FloppyO1/Floppy_soldering_station/CASE/components/power supply/under.jpg

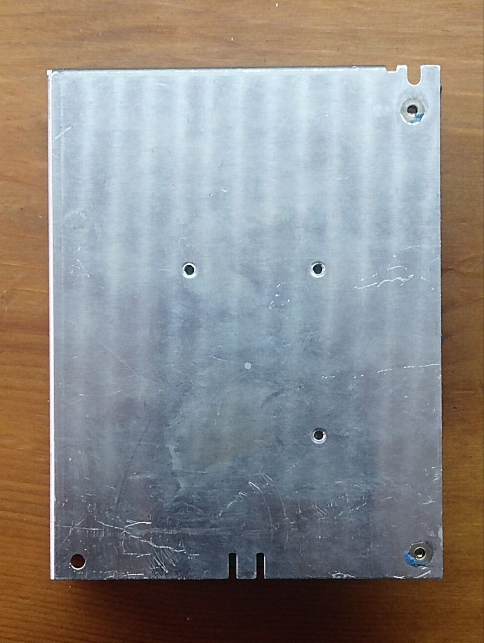
CASE/components/power supply/under.jpg
