FloppyO1/Floppy_soldering_station/CASE/components/GX16-4P.SLDPRT

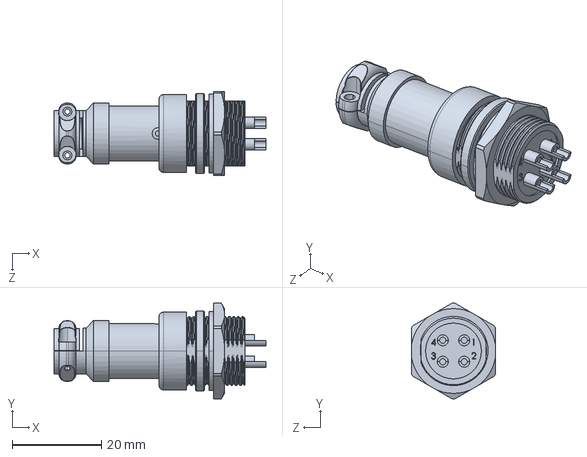
[picture p21: CAD file, 2024-06-17]
CASE/components/GX16-4P.SLDPRT
47.5 x 21.5 x 18.9 mm
