FloppyO1/Floppy_soldering_station/CASE/soldering iron holder.SLDPRT

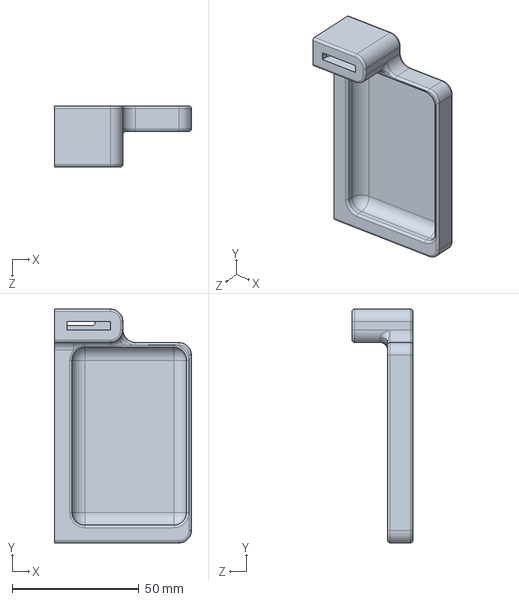
[picture p22: CAD file, 2024-06-17]
CASE/soldering iron holder.SLDPRT
54.0 x 92.2 x 24.0 mm
