FloppyO1/Floppy_soldering_station/CASE/components/C14 power plug.SLDPRT

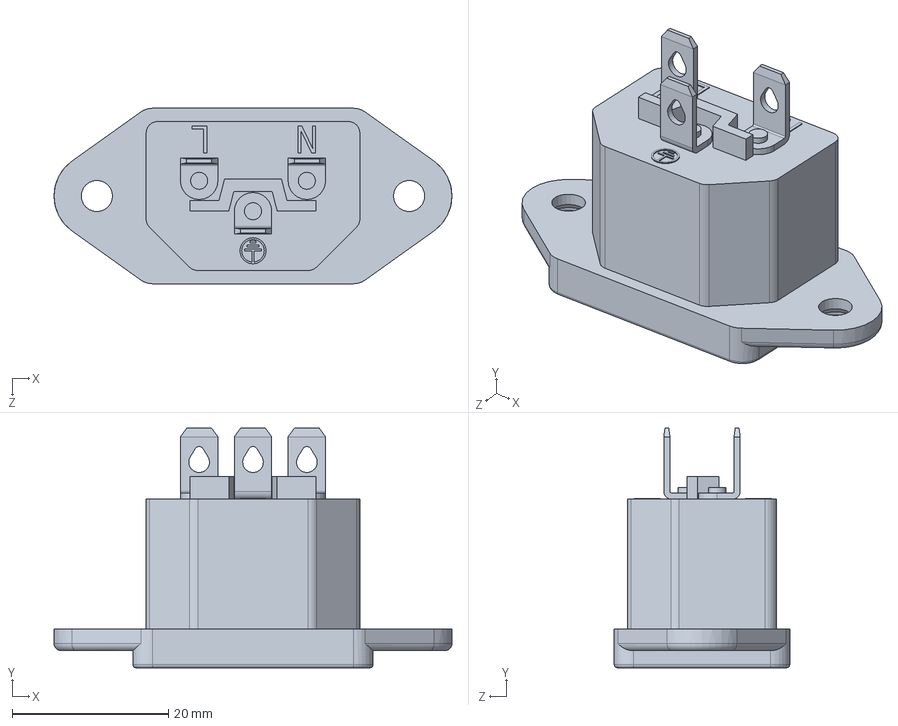
[picture p23: CAD file, 2024-06-17]
CASE/components/C14 power plug.SLDPRT
51.0 x 30.7 x 22.5 mm
