FloppyO1/Floppy_soldering_station/CASE/case 3.SLDPRT

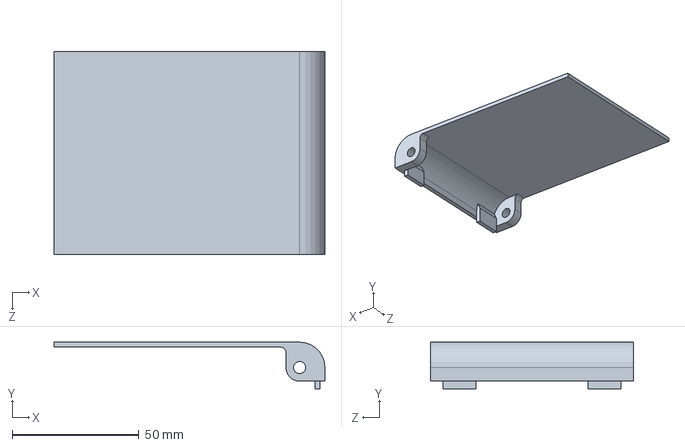
[picture p24: CAD file, 2024-06-17]
CASE/case 3.SLDPRT
106.7 x 18.4 x 80.0 mm
