FloppyO1/Floppy_soldering_station/CASE/components/rotary+encoder_17mm_hole_spc.SLDPRT

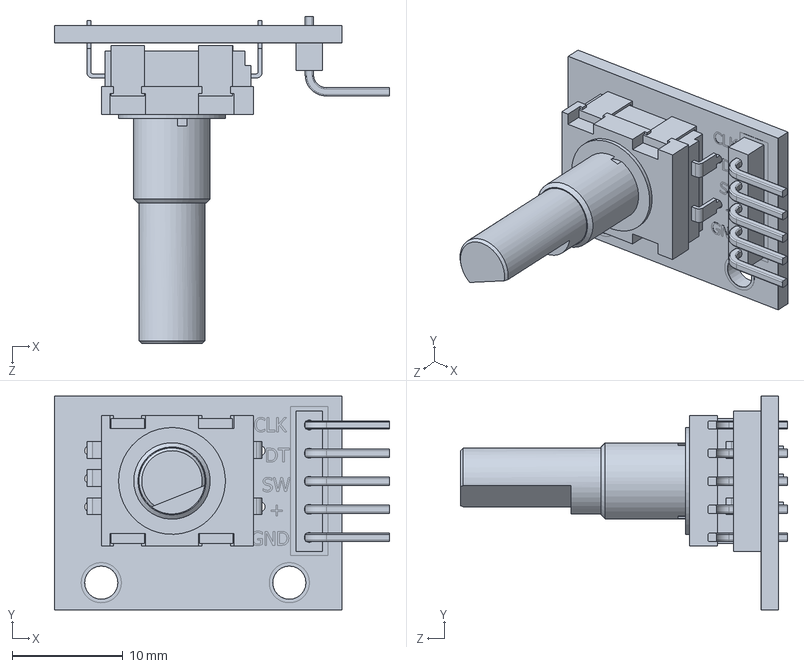
[picture p25: CAD file, 2024-06-17]
CASE/components/rotary+encoder_17mm_hole_spc.SLDPRT
30.3 x 19.3 x 29.6 mm
