FloppyO1/Floppy_soldering_station/CASE/case 1.SLDPRT

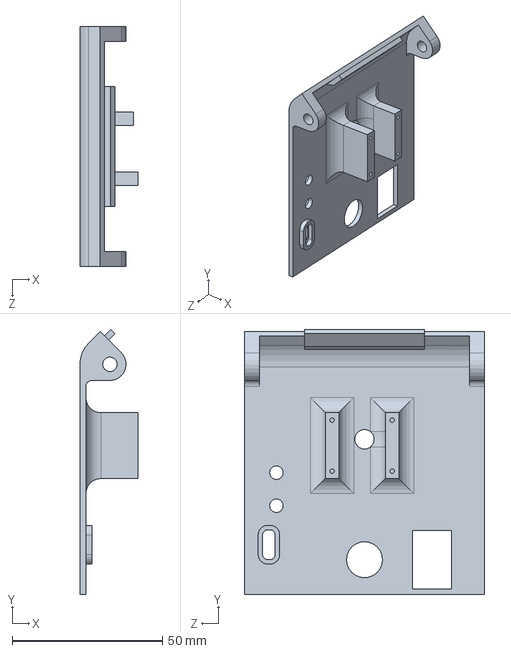
[picture p26: CAD file, 2024-06-17]
CASE/case 1.SLDPRT
19.4 x 88.3 x 80.0 mm
