FloppyO1/Floppy_soldering_station/CASE/case 2.SLDPRT

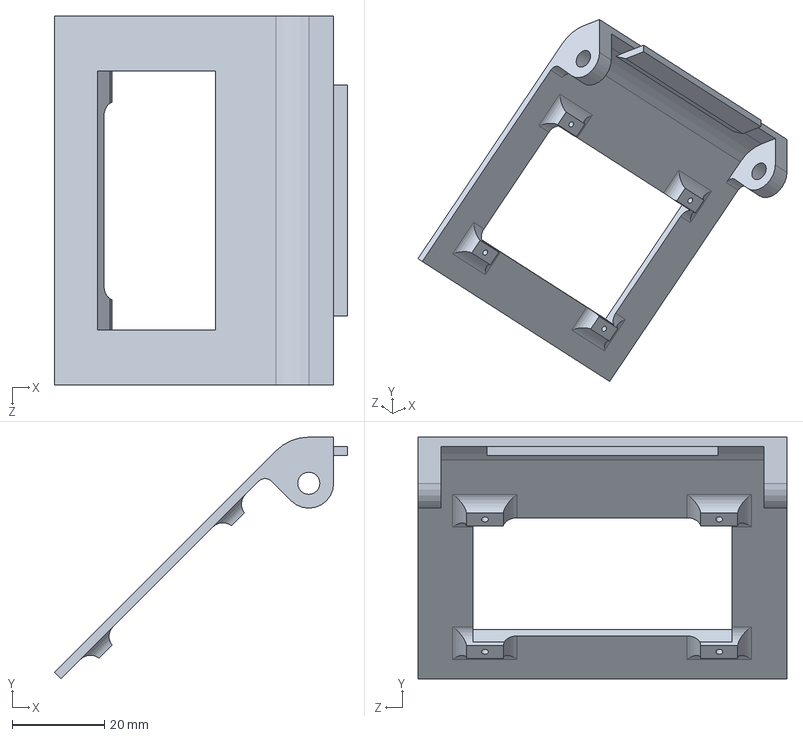
[picture p27: CAD file, 2024-06-17]
CASE/case 2.SLDPRT
63.5 x 52.4 x 80.0 mm
