FloppyO1/Floppy_soldering_station/CASE/case base.SLDPRT

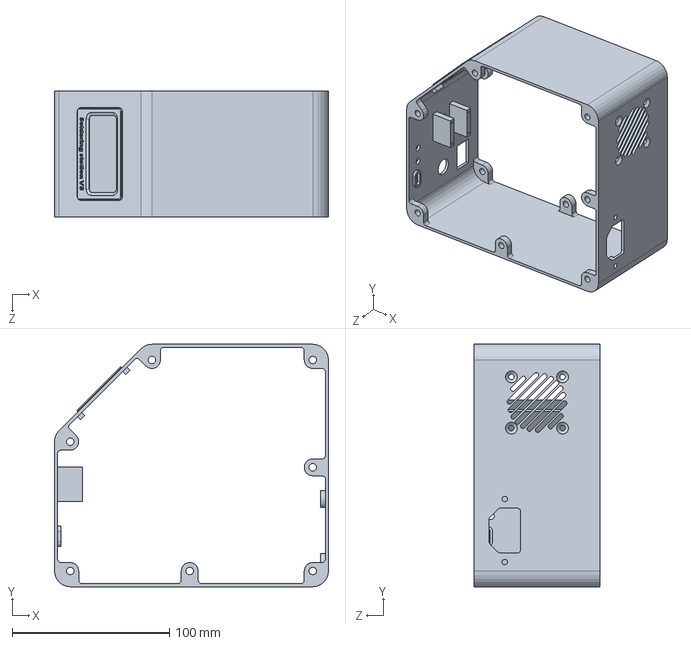
[picture p28: CAD file, 2024-06-17]
CASE/case base.SLDPRT
174.0 x 154.0 x 80.0 mm
