FloppyO1/Floppy_soldering_station/CASE/brass scourer holder.SLDPRT

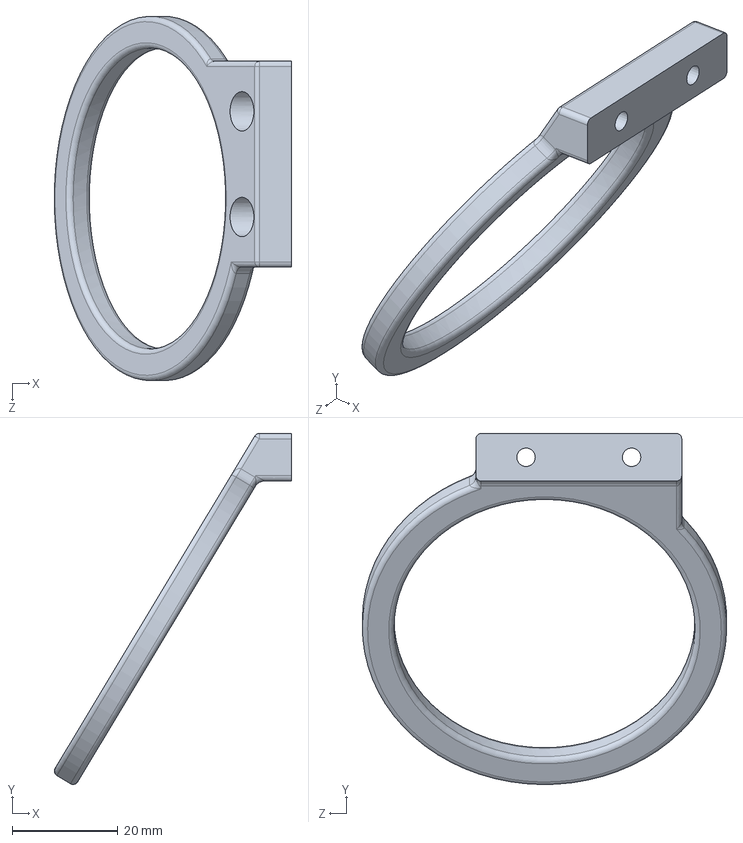
[picture p29: CAD file, 2024-06-17]
CASE/brass scourer holder.SLDPRT
45.0 x 66.5 x 69.0 mm
