FloppyO1/Floppy_soldering_station/CASE/case 5.SLDPRT

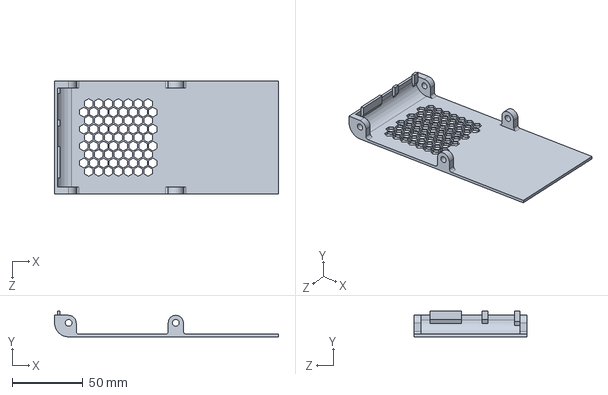
[picture p30: CAD file, 2024-06-17]
CASE/case 5.SLDPRT
158.6 x 18.4 x 80.0 mm
