FloppyO1/Floppy_soldering_station/CASE/knob.SLDPRT

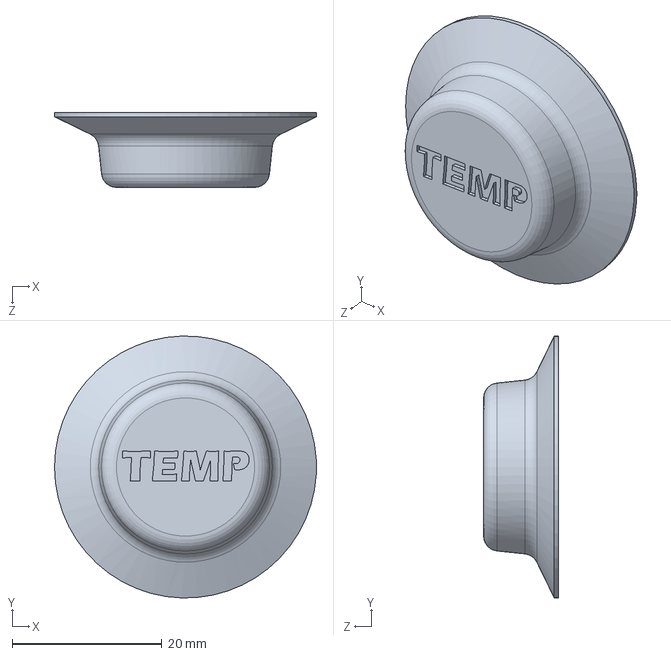
[picture p31: CAD file, 2024-06-17]
CASE/knob.SLDPRT
35.0 x 35.0 x 10.0 mm
